MakerM0/3Plus_v2/documents/images/1.png

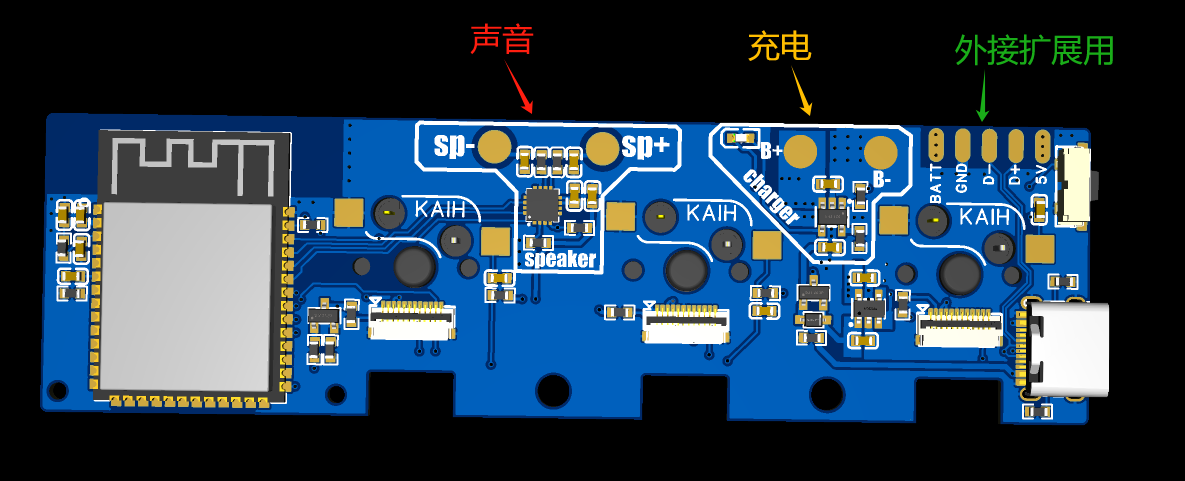
documents/images/1.png
