MakerM0/3Plus_v2/documents/images/002.jpg

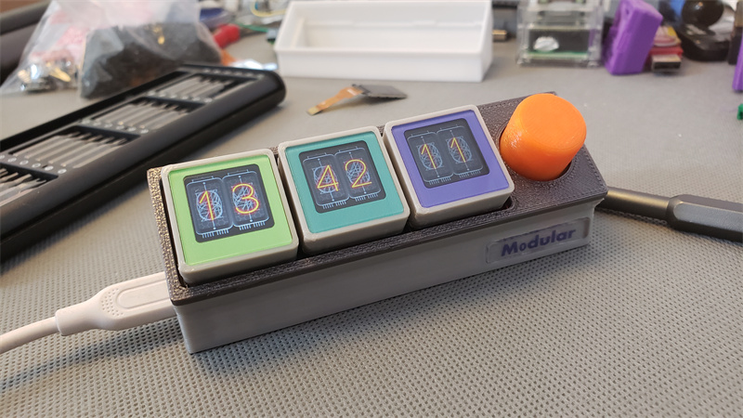
documents/images/002.jpg
