MakerM0/3Plus_v2/documents/images/003.jpg

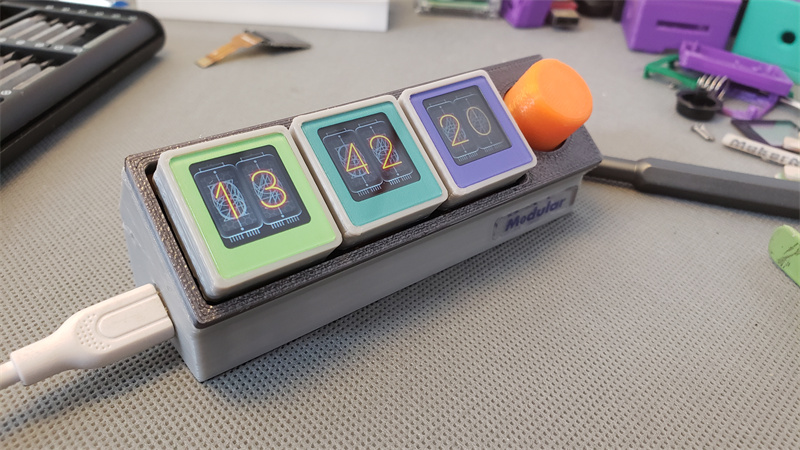
documents/images/003.jpg
