MakerM0/3Plus_v2/documents/images/004.jpg

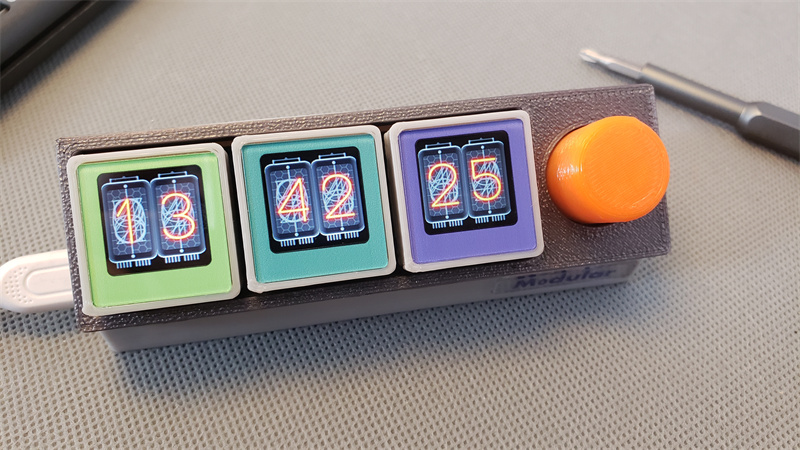
documents/images/004.jpg
