MakerM0/3Plus_v2/documents/images/005.jpg

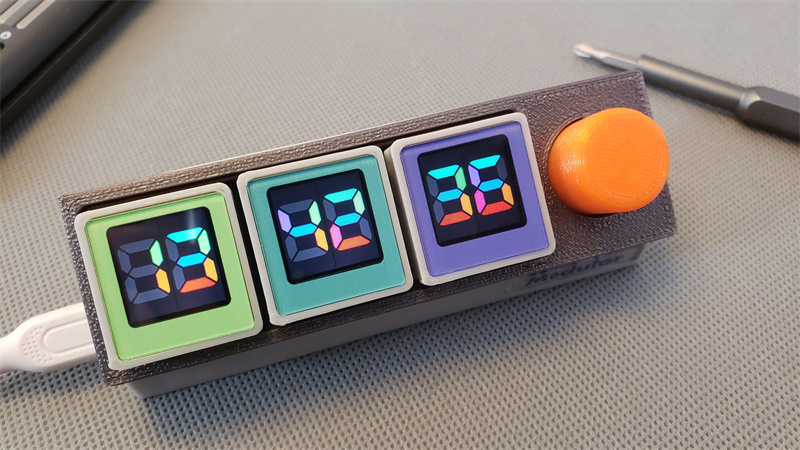
documents/images/005.jpg
