MakerM0/3Plus_v2/documents/images/006.jpg

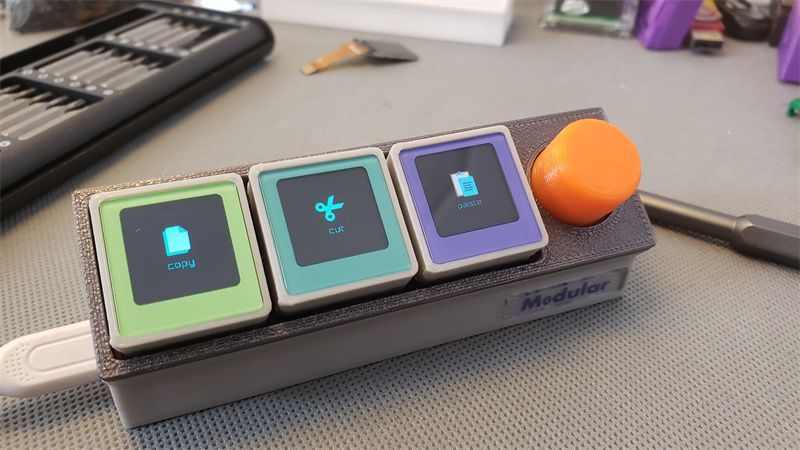
documents/images/006.jpg
