MakerM0/3Plus_v2/mechanical/stl/2.5/显示外壳 x3.stl

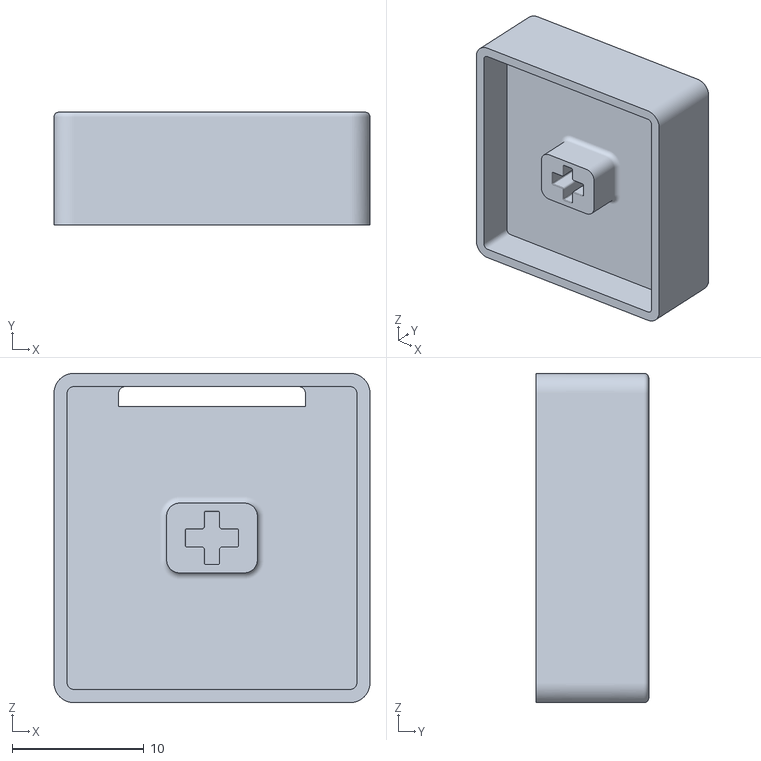
[picture p33: CAD file, 2023-11-21]
mechanical/stl/2.5/显示外壳 x3.stl
24.0 x 8.55 x 25.0
