MakerM0/3Plus_v2/mechanical/stl/Resin/盖板.stl

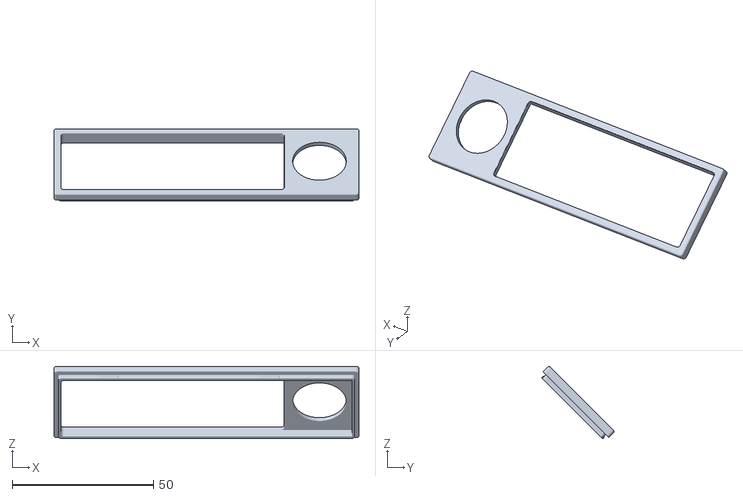
[picture p34: CAD file, 2023-11-28]
mechanical/stl/Resin/盖板.stl
108.0 x 25.6 x 25.6
